dc-power-supply/dc-power-supply/doc/components/transformer/1182L30.pdf

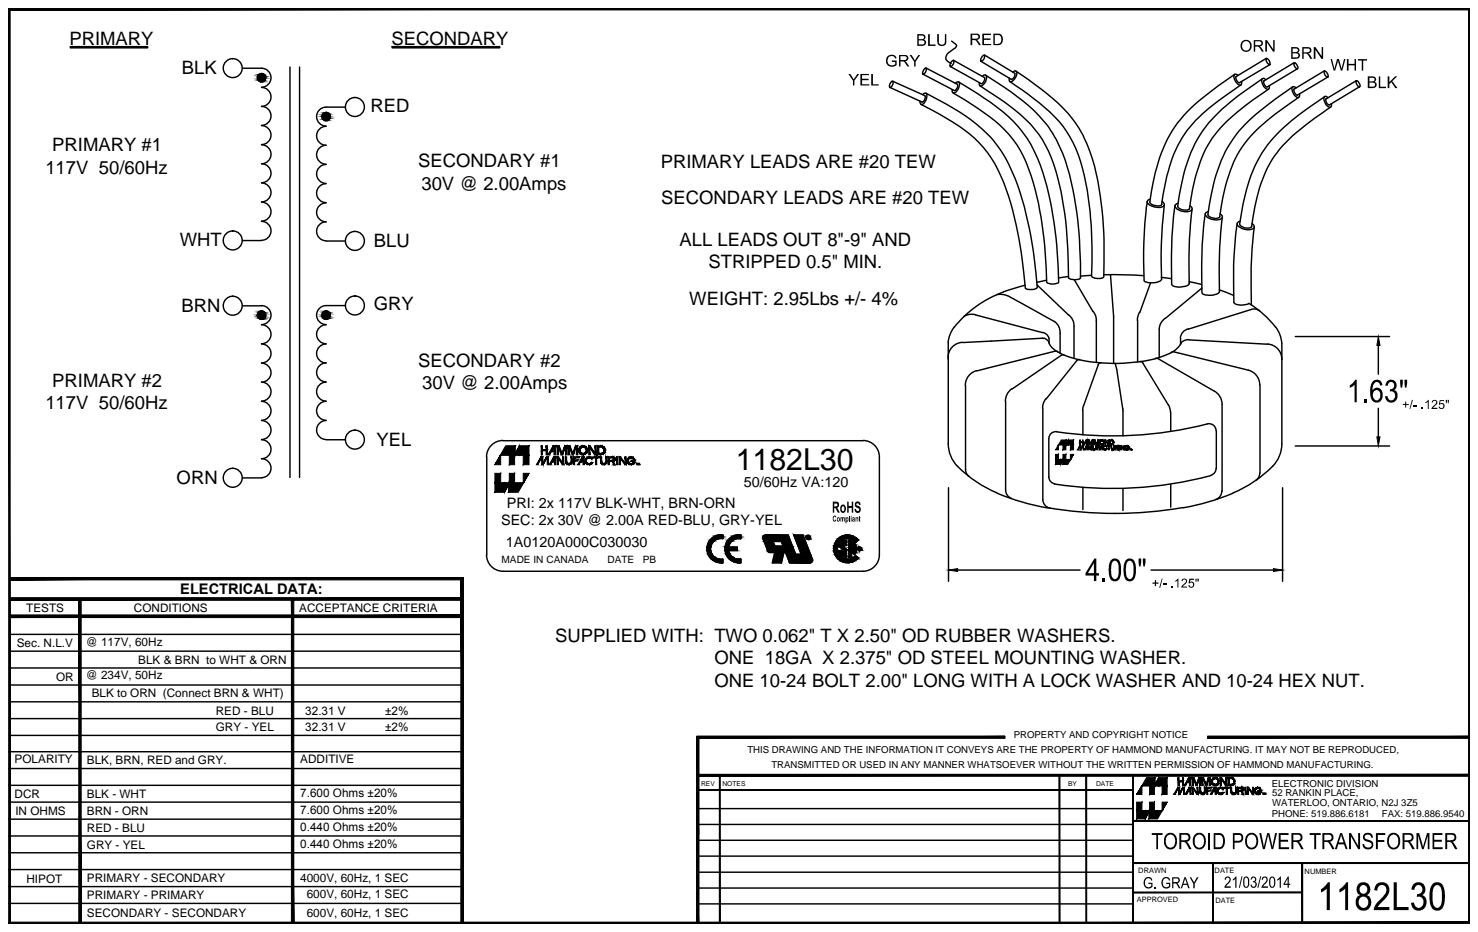
[picture p13: page 1]
